DLLSTART/CyberWand_Insta360/enclosure/output/v513_exploded.png

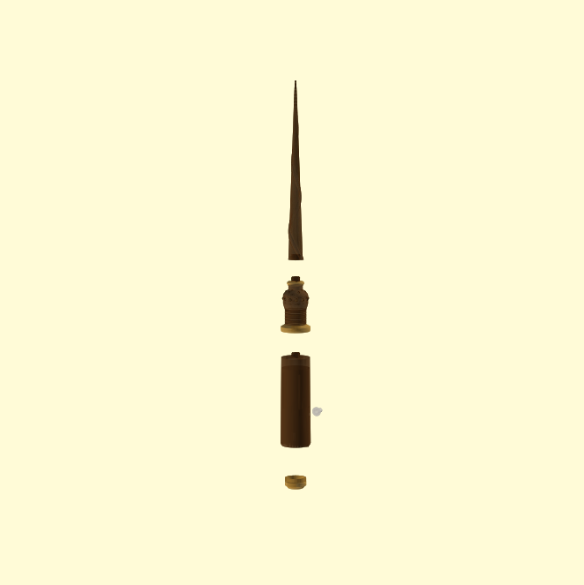
enclosure/output/v513_exploded.png
