DLLSTART/CyberWand_Insta360/enclosure/output/v513_handle_close.png

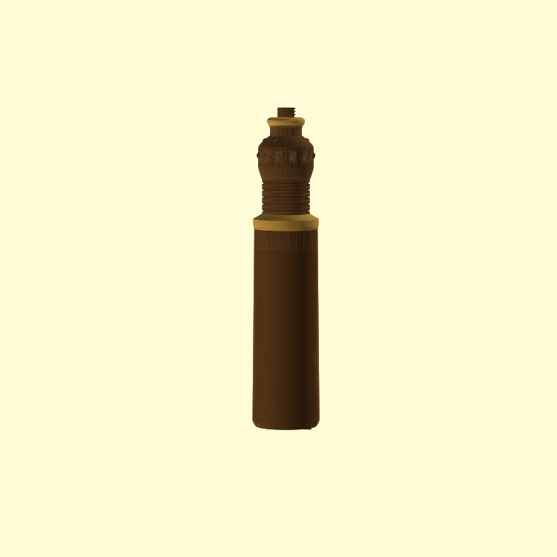
enclosure/output/v513_handle_close.png
