DLLSTART/CyberWand_Insta360/enclosure/output/v513_horizontal.png

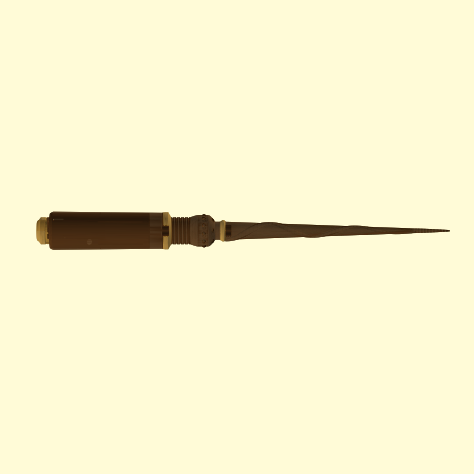
enclosure/output/v513_horizontal.png
