DLLSTART/CyberWand_Insta360/enclosure/output/v513_pommel.png

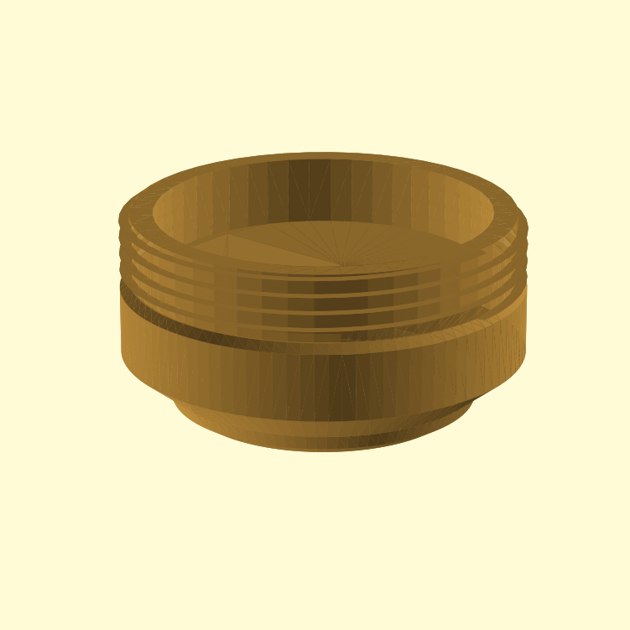
enclosure/output/v513_pommel.png
