DLLSTART/CyberWand_Insta360/archives/wand_reverse_v2.stl

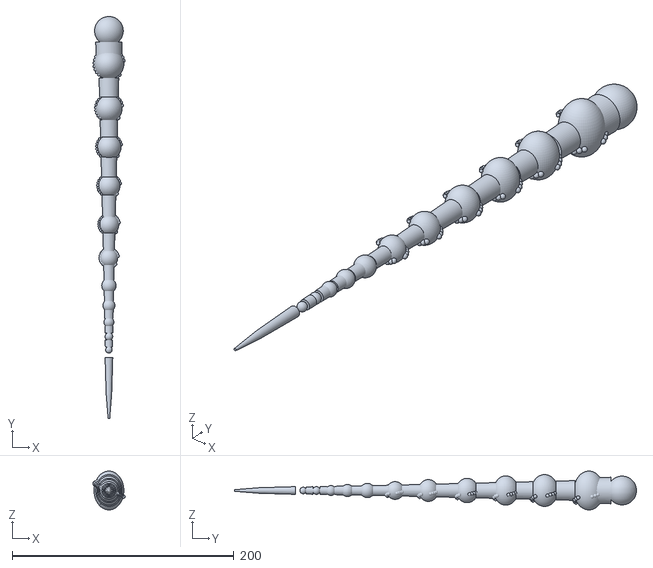
[picture p20: CAD file, 2026-04-11, an earlier design]
archives/wand_reverse_v2.stl
29.4 x 363.0 x 35.1
