DLLSTART/CyberWand_Insta360/archives/wand_reverse_v1.stl

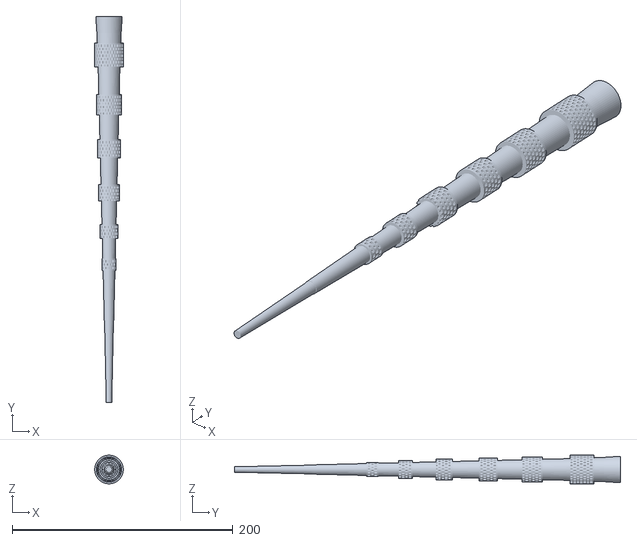
[picture p21: CAD file, 2026-04-11, an earlier design]
archives/wand_reverse_v1.stl
26.0 x 350.0 x 26.0
