DLLSTART/CyberWand_Insta360/enclosure/stl/cyberwand_head_top_old.stl

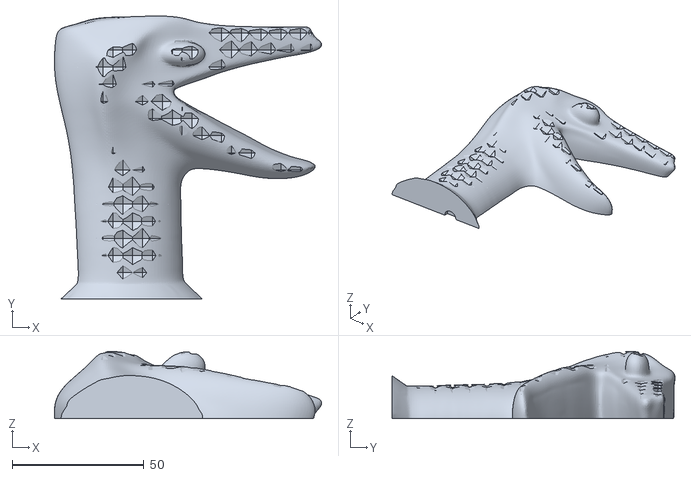
[picture p22: CAD file, 2026-05-18, an earlier design]
enclosure/stl/cyberwand_head_top_old.stl
101.4 x 107.4 x 25.5
