DLLSTART/CyberWand_Insta360/enclosure/output/v513_print_orient_A.png

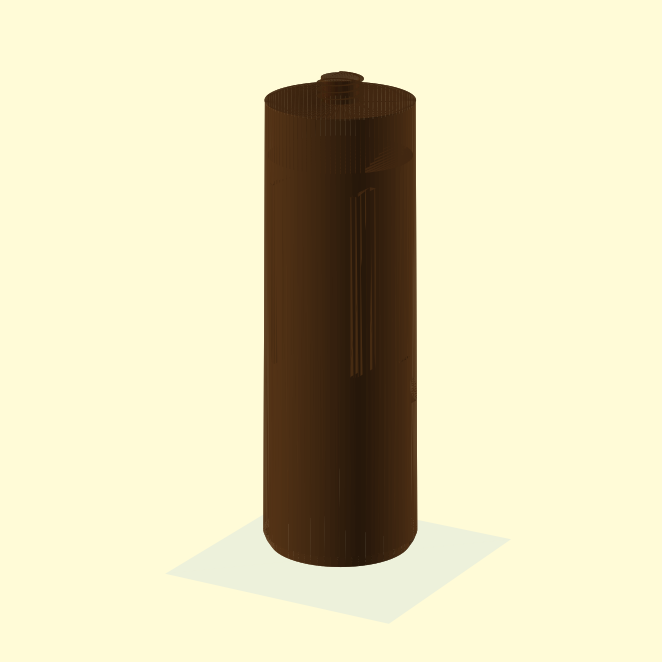
enclosure/output/v513_print_orient_A.png
