DLLSTART/CyberWand_Insta360/enclosure/output/v513_print_orient_B.png

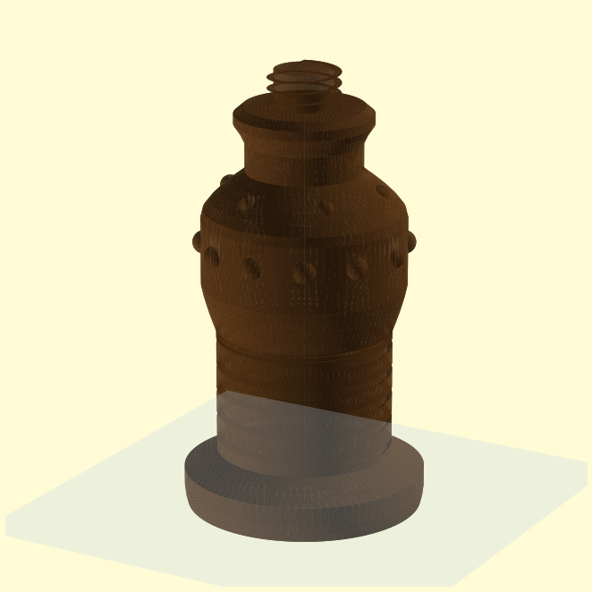
enclosure/output/v513_print_orient_B.png
