DLLSTART/CyberWand_Insta360/enclosure/output/v513_print_orient_E.png

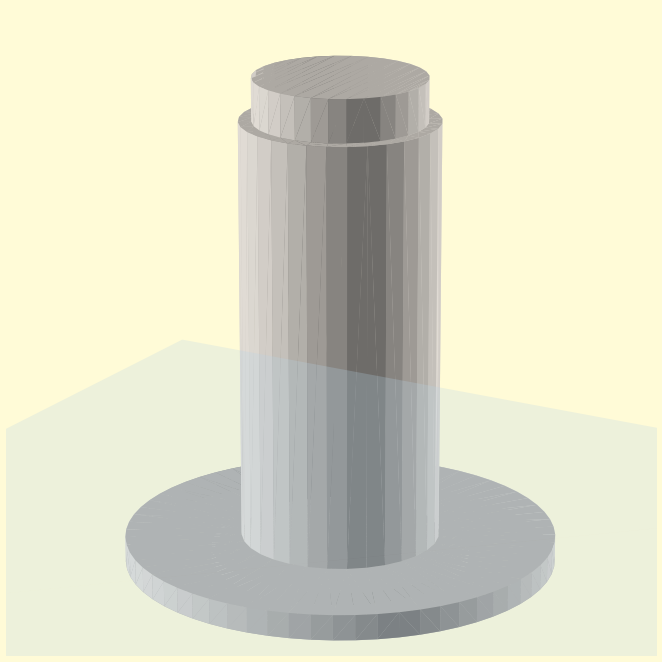
enclosure/output/v513_print_orient_E.png
