DLLSTART/CyberWand_Insta360/Software/weights.h

#include "nnom.h"

/* Weights, bias and Q format */
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

#define TENSOR_CONV1D_1_KERNEL_0_DEC_BITS {8}

#define TENSOR_CONV1D_1_BIAS_0 {111, -28, 16, 13, -38, -58, 86, -28, -36, 109, 13, -18, -6, -14, -15}

#define TENSOR_CONV1D_1_BIAS_0_DEC_BITS {11}

#define CONV1D_1_BIAS_LSHIFT {0}

#define CONV1D_1_OUTPUT_RSHIFT {8}

#define TENSOR_DENSE_KERNEL_0 {0, -28, -19, 15, 12, 9, -23, -13, -46, -40, 15, 21, -31, -19, 18, 43, -38, 29, -4, 39, -28, 16, -22, -18, 47, 27, -32, -34, -13, 2, 9, 19, -1, 35, -30, 9, 46, 5, -44, 50, 11, -43, -24, -41, 34, -55, -37, 7, 15, -26, 41, 28, 7, 5, -18, 41, -31, 22, 0, -25, -44, 19, -29, 11, -16, 0, -27, 26, -29, 13, -15, 35, 16, 29, -38, 12, -22, -19, 11, 26, 18, -29, -9, -7, 31, -5, 23, 25, -17, -25, -28, -31, -10, 15, 5, 27, 11, 22, 35, -15, -40, 9, 22, -11, -26, 0, 5, 38, 19, 33, 3, 39, 4, 12, -18, -6, -22, 32, 19, -24, 26, 29, -10, 17, 15, 10, -19, -38, 15, 3, 10, 5, -22, 2, 27, -27, 9, 39, -2, 31, 42, -32, 23, 23, -7, -24, -18, 5, 3, 7, -12, 35, 20, 35, 17, 17, -37, -25, 8, 6, -31, 33, -10, -50, -23, -15, 27, 37, 48, -13, 33, 9, 5, 18, -18, 33, -12, -40, 28, 22, -10, 33, -10, 14, -44, 43, -22, 24, -50, -6, -6, -22, 22, -11, 23, -14, 11, 11, 47, 17, -40, 17, -25, -11, 21, -11, 2, 21, -4, 5, -16, 0, -7, 22, -1, -34, -27, 34, 10, 9, 36, -12, 19, 0, 30, 30, 7, -12, -10, 17, 14, 5, 12, -32, 30, 15, 30, 44, 21, -6, 10, -4, -16, -20, 9, 3, 11, -55, 26, 23, 0, 21, -25, -1, 31, 26, 22, -22, -8, -38, -39, 12, -28, 52, -17, -34, -10, 5, 31, 27, -35, -1, -8, 22, 32, 14, 9, 24, -8, 11, 36, 10, 22, 1, 1, 27, -9, 31, 10, -9, 18, -17, 19, 7, -12, -38, -8, -44, -10, -17, 4, -22, -44, -18, 15, 24, -22, -34, -22, -45, 12, 22, 33, -1, 13, 29, -46, 3, -9, 39, 11, 30, 17, 28, 38, 22, -2, 8, -45, 10, -33, 37, 16, 41, 22, 14, 15, -35, 19, 17, -9, -48, -27, -30, 35, 1, -11, -7, -26,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
-18, 11, 16, 49, 1, -2, 4, -40, -31, 20, 4, -19, -2, -27, 20, 8, -6, 29, 50, -33, 6, -1, -47, -20, 11, -14, -29, -33, -7, -38, 40, 2, 2, 24, -26, 32, 26, -23, -38, -2, -18, 37, 14, -2, -3, -19, -29, -23, -1, -28, -11, -6, 13, 8, -19, 9, 9, 4, 30, -9, 31, 20, 24, 0, 21, -4, 12, -12, 26, 26, 7, 27, -22, -21, 24, -19, -4, 34, 9, -23, -12, 38, 23, 16, 14, -18, 33, 8, -3, -44, 34, -36, 42, 18, -19, 25, 34, -3, 31, 26, -27, 10, -6, -4, -24, 11, -12, -3, 10, -1, 24, 33, 0, 5, 23, -15, -24, -7, -1, 16}

#define TENSOR_DENSE_KERNEL_0_DEC_BITS {8}

#define TENSOR_DENSE_BIAS_0 {-26, -21, -85, -5, -99, 68}

#define TENSOR_DENSE_BIAS_0_DEC_BITS {11}

#define DENSE_BIAS_LSHIFT {0}

#define DENSE_OUTPUT_RSHIFT {7}


/* output q format for each layer */
#define INPUT_1_OUTPUT_DEC 4
#define INPUT_1_OUTPUT_OFFSET 0
#define CONV1D_OUTPUT_DEC 3
#define CONV1D_OUTPUT_OFFSET 0
#define LEAKY_RE_LU_OUTPUT_DEC 3
#define LEAKY_RE_LU_OUTPUT_OFFSET 0
#define CONV1D_1_OUTPUT_DEC 3
#define CONV1D_1_OUTPUT_OFFSET 0
#define LEAKY_RE_LU_1_OUTPUT_DEC 3
#define LEAKY_RE_LU_1_OUTPUT_OFFSET 0
#define FLATTEN_OUTPUT_DEC 3
#define FLATTEN_OUTPUT_OFFSET 0
#define DENSE_OUTPUT_DEC 4
#define DENSE_OUTPUT_OFFSET 0
#define DROPOUT_OUTPUT_DEC 4
#define DROPOUT_OUTPUT_OFFSET 0
#define SOFTMAX_OUTPUT_DEC 7
#define SOFTMAX_OUTPUT_OFFSET 0

/* bias shift and output shift for none-weighted layer */

/* tensors and configurations for each layer */
static int8_t nnom_input_data[900] = {0};

const nnom_shape_data_t tensor_input_1_dim[] = {150, 6};
const nnom_qformat_param_t tensor_input_1_dec[] = {4};
const nnom_qformat_param_t tensor_input_1_offset[] = {0};
const nnom_tensor_t tensor_input_1 = {
    .p_data = (void*)nnom_input_data,
    .dim = (nnom_shape_data_t*)tensor_input_1_dim,
    .q_dec = (nnom_qformat_param_t*)tensor_input_1_dec,
    .q_offset = (nnom_qformat_param_t*)tensor_input_1_offset,
    .qtype = NNOM_QTYPE_PER_TENSOR,
    .num_dim = 2,
    .bitwidth = 8
};

const nnom_io_config_t input_1_config = {
    .super = {.name = "input_1"},
    .tensor = (nnom_tensor_t*)&tensor_input_1
};
const int8_t tensor_conv1d_kernel_0_data[] = TENSOR_CONV1D_KERNEL_0;

const nnom_shape_data_t tensor_conv1d_kernel_0_dim[] = {3, 6, 30};
const nnom_qformat_param_t tensor_conv1d_kernel_0_dec[] = TENSOR_CONV1D_KERNEL_0_DEC_BITS;
const nnom_qformat_param_t tensor_conv1d_kernel_0_offset[] = {0};
const nnom_tensor_t tensor_conv1d_kernel_0 = {
    .p_data = (void*)tensor_conv1d_kernel_0_data,
    .dim = (nnom_shape_data_t*)tensor_conv1d_kernel_0_dim,
    .q_dec = (nnom_qformat_param_t*)tensor_conv1d_kernel_0_dec,
    .q_offset = (nnom_qformat_param_t*)tensor_conv1d_kernel_0_offset,
    .qtype = NNOM_QTYPE_PER_TENSOR,
    .num_dim = 3,
    .bitwidth = 8
};
const int8_t tensor_conv1d_bias_0_data[] = TENSOR_CONV1D_BIAS_0;

const nnom_shape_data_t tensor_conv1d_bias_0_dim[] = {30};
const nnom_qformat_param_t tensor_conv1d_bias_0_dec[] = TENSOR_CONV1D_BIAS_0_DEC_BITS;
const nnom_qformat_param_t tensor_conv1d_bias_0_offset[] = {0};
const nnom_tensor_t tensor_conv1d_bias_0 = {
    .p_data = (void*)tensor_conv1d_bias_0_data,
    .dim = (nnom_shape_data_t*)tensor_conv1d_bias_0_dim,
    .q_dec = (nnom_qformat_param_t*)tensor_conv1d_bias_0_dec,
    .q_offset = (nnom_qformat_param_t*)tensor_conv1d_bias_0_offset,
    .qtype = NNOM_QTYPE_PER_TENSOR,
    .num_dim = 1,
    .bitwidth = 8
};

const nnom_qformat_param_t conv1d_output_shift[] = CONV1D_OUTPUT_RSHIFT;
const nnom_qformat_param_t conv1d_bias_shift[] = CONV1D_BIAS_LSHIFT;
const nnom_conv2d_config_t conv1d_config = {
    .super = {.name = "conv1d"},
    .qtype = NNOM_QTYPE_PER_TENSOR,
    .weight = (nnom_tensor_t*)&tensor_conv1d_kernel_0,
    .bias = (nnom_tensor_t*)&tensor_conv1d_bias_0,
    .output_shift = (nnom_qformat_param_t *)&conv1d_output_shift, 
    .bias_shift = (nnom_qformat_param_t *)&conv1d_bias_shift, 
    .filter_size = 30,
    .kernel_size = {3},
    .stride_size = {3},
    .padding_size = {0, 0},
    .dilation_size = {1},
    .padding_type = PADDING_SAME
};
const int8_t tensor_conv1d_1_kernel_0_data[] = TENSOR_CONV1D_1_KERNEL_0;

const nnom_shape_data_t tensor_conv1d_1_kernel_0_dim[] = {3, 30, 15};
const nnom_qformat_param_t tensor_conv1d_1_kernel_0_dec[] = TENSOR_CONV1D_1_KERNEL_0_DEC_BITS;
const nnom_qformat_param_t tensor_conv1d_1_kernel_0_offset[] = {0};
const nnom_tensor_t tensor_conv1d_1_kernel_0 = {
    .p_data = (void*)tensor_conv1d_1_kernel_0_data,
    .dim = (nnom_shape_data_t*)tensor_conv1d_1_kernel_0_dim,
    .q_dec = (nnom_qformat_param_t*)tensor_conv1d_1_kernel_0_dec,
    .q_offset = (nnom_qformat_param_t*)tensor_conv1d_1_kernel_0_offset,
    .qtype = NNOM_QTYPE_PER_TENSOR,
    .num_dim = 3,
    .bitwidth = 8
};
const int8_t tensor_conv1d_1_bias_0_data[] = TENSOR_CONV1D_1_BIAS_0;

const nnom_shape_data_t tensor_conv1d_1_bias_0_dim[] = {15};
const nnom_qformat_param_t tensor_conv1d_1_bias_0_dec[] = TENSOR_CONV1D_1_BIAS_0_DEC_BITS;
const nnom_qformat_param_t tensor_conv1d_1_bias_0_offset[] = {0};
const nnom_tensor_t tensor_conv1d_1_bias_0 = {
    .p_data = (void*)tensor_conv1d_1_bias_0_data,
    .dim = (nnom_shape_data_t*)tensor_conv1d_1_bias_0_dim,
    .q_dec = (nnom_qformat_param_t*)tensor_conv1d_1_bias_0_dec,
    .q_offset = (nnom_qformat_param_t*)tensor_conv1d_1_bias_0_offset,
    .qtype = NNOM_QTYPE_PER_TENSOR,
    .num_dim = 1,
    .bitwidth = 8
};

const nnom_qformat_param_t conv1d_1_output_shift[] = CONV1D_1_OUTPUT_RSHIFT;
const nnom_qformat_param_t conv1d_1_bias_shift[] = CONV1D_1_BIAS_LSHIFT;
const nnom_conv2d_config_t conv1d_1_config = {
    .super = {.name = "conv1d_1"},
    .qtype = NNOM_QTYPE_PER_TENSOR,
    .weight = (nnom_tensor_t*)&tensor_conv1d_1_kernel_0,
    .bias = (nnom_tensor_t*)&tensor_conv1d_1_bias_0,
    .output_shift = (nnom_qformat_param_t *)&conv1d_1_output_shift, 
    .bias_shift = (nnom_qformat_param_t *)&conv1d_1_bias_shift, 
    .filter_size = 15,
    .kernel_size = {3},
    .stride_size = {3},
    .padding_size = {0, 0},
    .dilation_size = {1},
    .padding_type = PADDING_SAME
};

const nnom_flatten_config_t flatten_config = {
    .super = {.name = "flatten"}
};
const int8_t tensor_dense_kernel_0_data[] = TENSOR_DENSE_KERNEL_0;

const nnom_shape_data_t tensor_dense_kernel_0_dim[] = {255, 6};
const nnom_qformat_param_t tensor_dense_kernel_0_dec[] = TENSOR_DENSE_KERNEL_0_DEC_BITS;
const nnom_qformat_param_t tensor_dense_kernel_0_offset[] = {0};
const nnom_tensor_t tensor_dense_kernel_0 = {
    .p_data = (void*)tensor_dense_kernel_0_data,
    .dim = (nnom_shape_data_t*)tensor_dense_kernel_0_dim,
    .q_dec = (nnom_qformat_param_t*)tensor_dense_kernel_0_dec,
    .q_offset = (nnom_qformat_param_t*)tensor_dense_kernel_0_offset,
    .qtype = NNOM_QTYPE_PER_TENSOR,
    .num_dim = 2,
    .bitwidth = 8
};
const int8_t tensor_dense_bias_0_data[] = TENSOR_DENSE_BIAS_0;

const nnom_shape_data_t tensor_dense_bias_0_dim[] = {6};
const nnom_qformat_param_t tensor_dense_bias_0_dec[] = TENSOR_DENSE_BIAS_0_DEC_BITS;
const nnom_qformat_param_t tensor_dense_bias_0_offset[] = {0};
const nnom_tensor_t tensor_dense_bias_0 = {
    .p_data = (void*)tensor_dense_bias_0_data,
    .dim = (nnom_shape_data_t*)tensor_dense_bias_0_dim,
    .q_dec = (nnom_qformat_param_t*)tensor_dense_bias_0_dec,
    .q_offset = (nnom_qformat_param_t*)tensor_dense_bias_0_offset,
    .qtype = NNOM_QTYPE_PER_TENSOR,
    .num_dim = 1,
    .bitwidth = 8
};

const nnom_qformat_param_t dense_output_shift[] = DENSE_OUTPUT_RSHIFT;
const nnom_qformat_param_t dense_bias_shift[] = DENSE_BIAS_LSHIFT;
const nnom_dense_config_t dense_config = {
    .super = {.name = "dense"},
    .qtype = NNOM_QTYPE_PER_TENSOR,
    .weight = (nnom_tensor_t*)&tensor_dense_kernel_0,
    .bias = (nnom_tensor_t*)&tensor_dense_bias_0,
    .output_shift = (nnom_qformat_param_t *)&dense_output_shift,
    .bias_shift = (nnom_qformat_param_t *)&dense_bias_shift
};

const nnom_softmax_config_t softmax_config = {
    .super = {.name = "softmax"}
};
static int8_t nnom_output_data[6] = {0};

const nnom_shape_data_t tensor_output0_dim[] = {6};
const nnom_qformat_param_t tensor_output0_dec[] = {SOFTMAX_OUTPUT_DEC};
const nnom_qformat_param_t tensor_output0_offset[] = {0};
const nnom_tensor_t tensor_output0 = {
    .p_data = (void*)nnom_output_data,
    .dim = (nnom_shape_data_t*)tensor_output0_dim,
    .q_dec = (nnom_qformat_param_t*)tensor_output0_dec,
    .q_offset = (nnom_qformat_param_t*)tensor_output0_offset,
    .qtype = NNOM_QTYPE_PER_TENSOR,
    .num_dim = 1,
    .bitwidth = 8
};

const nnom_io_config_t output0_config = {
    .super = {.name = "output0"},
    .tensor = (nnom_tensor_t*)&tensor_output0
};
/* model version */
#define NNOM_MODEL_VERSION (10000*0 + 100*4 + 3)

/* nnom model */
static nnom_model_t* nnom_model_create(void)
{
	static nnom_model_t model;
	nnom_layer_t* layer[9];

	check_model_version(NNOM_MODEL_VERSION);
	new_model(&model);

	layer[0] = input_s(&input_1_config);
	layer[1] = model.hook(conv2d_s(&conv1d_config), layer[0]);
	layer[2] = model.active(act_leaky_relu(0.300000f), layer[1]);
	layer[3] = model.hook(conv2d_s(&conv1d_1_config), layer[2]);
	layer[4] = model.active(act_leaky_relu(0.300000f), layer[3]);
	layer[5] = model.hook(flatten_s(&flatten_config), layer[4]);
	layer[6] = model.hook(dense_s(&dense_config), layer[5]);
	layer[7] = model.hook(softmax_s(&softmax_config), layer[6]);
	layer[8] = model.hook(output_s(&output0_config), layer[7]);
	model_compile(&model, layer[0], layer[8]);
	return &model;
}
